unspecworks/delta-omega/case/delta_omega_rev2_left_thread.png

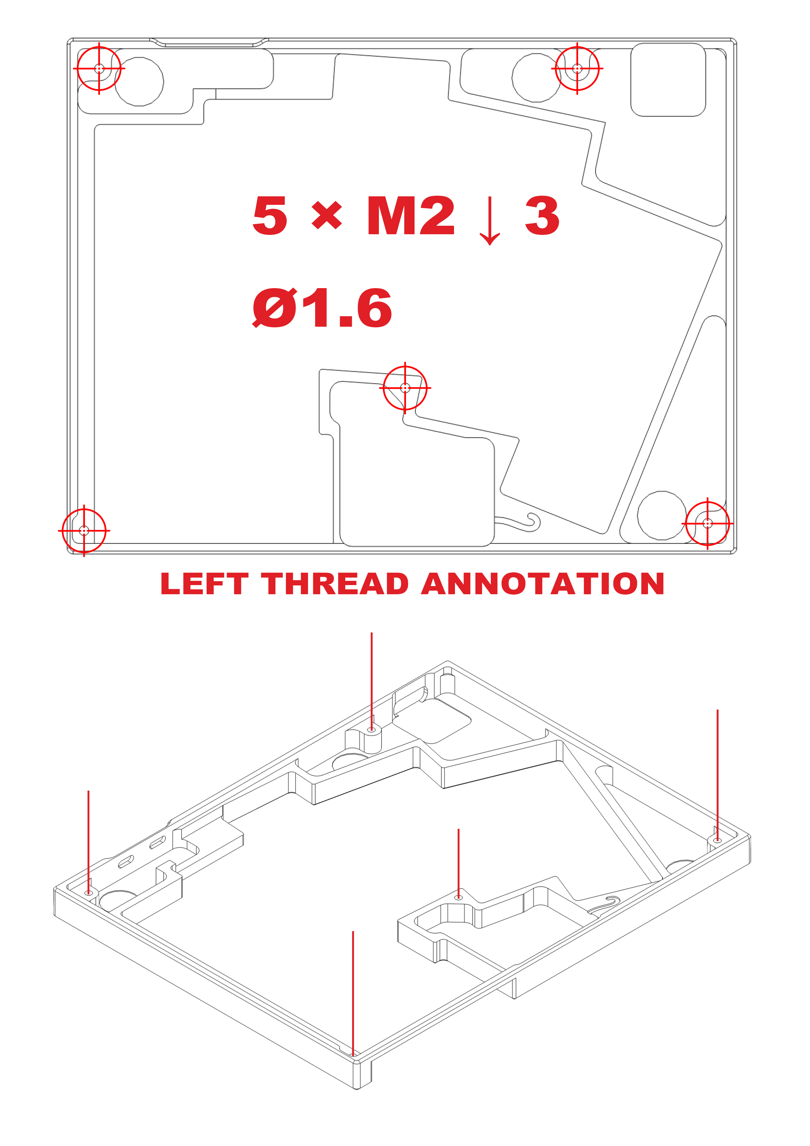
case/delta_omega_rev2_left_thread.png
