unspecworks/delta-omega/case/delta_omega_rev2_right_thread.png

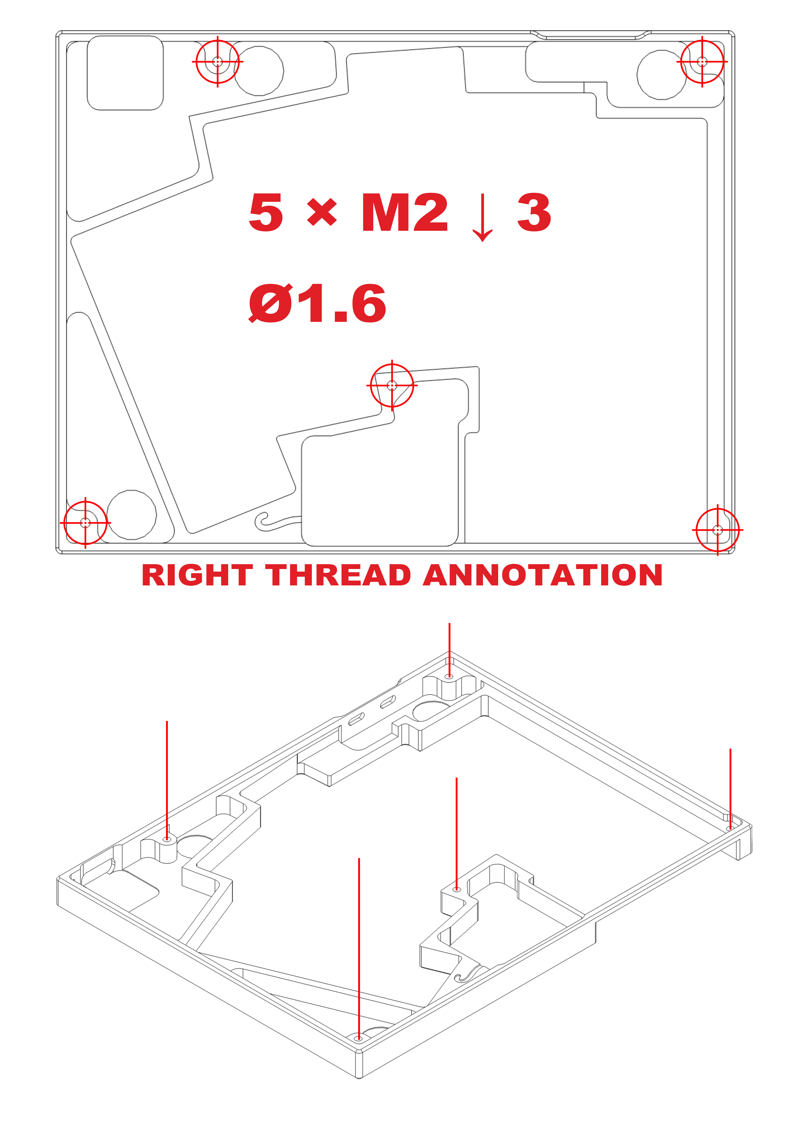
case/delta_omega_rev2_right_thread.png
